lzpel/cloudmama/esp32/components/esp8266-google-home-notifier/src/esp8266-google-home-notifier.h

#ifndef GoogleHomeNotifier_h
#define GoogleHomeNotifier_h

#include <pb.h>
#include <pb_encode.h>
#include <pb_decode.h>
#include <cast_channel.pb.h>

#include <WiFiClientSecure.h>

#include "esp_sdk_version.h"
#ifdef ARDUINO_ARCH_ESP8266
#include <ESP8266mDNS.h>
#elif defined ARDUINO_ARCH_ESP32
#include <ESPmDNS.h>
#else
#error "ARDUINO_ARCH_ESP8266 or ARDUINO_ARCH_ESP32 has to be defined."
#endif

//#include <google-tts.h>

#define LIB_NAME "GoogleHomeNotifier for ESP8266"
#define LIB_VERSION "0.1"

#define APP_ID "CC1AD845"

#define SOURCE_ID "sender-0"
#define DESTINATION_ID "receiver-0"

#define CASTV2_NS_CONNECTION "urn:x-cast:com.google.cast.tp.connection"
#define CASTV2_NS_HEARTBEAT "urn:x-cast:com.google.cast.tp.heartbeat"
#define CASTV2_NS_RECEIVER "urn:x-cast:com.google.cast.receiver"
#define CASTV2_NS_MEDIA "urn:x-cast:com.google.cast.media"

#define CASTV2_DATA_CONNECT "{\"type\":\"CONNECT\"}"
#define CASTV2_DATA_PING "{\"type\":\"PING\"}"
#define CASTV2_DATA_LAUNCH "{\"type\":\"LAUNCH\",\"appId\":\"%s\",\"requestId\":1}"
#define CASTV2_DATA_LOAD "{\"type\":\"LOAD\",\"autoplay\":true,\"currentTime\":0,\"activeTrackIds\":[],\"repeatMode\":\"REPEAT_OFF\",\"media\":{\"contentId\":\"%s\",\"contentType\":\"audio/mp3\",\"streamType\":\"BUFFERED\"},\"requestId\":1}"

typedef class GoogleHomeNotifier {

private:
  char m_transportid[40] = {0};
  char m_clientid[40] = {0};

  //TTS tts;
  WiFiClientSecure* m_client = nullptr;
  boolean m_clientCreated = false;
  IPAddress m_ipaddress;
  uint16_t m_port = 0;
  char m_locale[10] = "en";
  char m_name[128] = "";
  char m_lastError[128] = "";
  bool m_mDNSIsRunning = false;
  static bool encode_string(pb_ostream_t *stream, const pb_field_t *field, void * const *arg);
  static bool decode_string(pb_istream_t *stream, const pb_field_t *field, void **arg);
  boolean connect();
  boolean _play(const char *mp3url);
  void disconnect();
  void setLastError(const char *lastError);
  boolean sendMessage(const char *sourceId, const char *destinationId, const char *ns, const char *data);
  boolean cast(const char *phrase, const char *mp3Url, WiFiClientSecure* pClient = nullptr);

public:
  boolean ip(IPAddress ip, const char *locale = "en", uint16_t port = 8009);
  boolean device(const char *name, const char *locale = "en", int to = 10000);
  boolean notify(const char *phrase, WiFiClientSecure* pClient = nullptr);
  boolean play(const char *mp3Url, WiFiClientSecure* pClient = nullptr);
  const IPAddress getIPAddress();
  const uint16_t getPort();
  const char * getLastError();

} GoogleHomeNotifier;

#endif
