lzpel/cloudmama/esp32/components/esp8266-google-home-notifier/src/esp_sdk_version.h

#ifndef ESP_SDK_VERSION_h
#define ESP_SDK_VERSION_h

//#include <core_version.h>

//#if defined(ARDUINO_ESP32_RELEASE_1_0_4) || defined(ARDUINO_ESP32_RELEASE_1_0_3) || defined(ARDUINO_ESP32_RELEASE_1_0_2) || defined(ARDUINO_ESP32_RELEASE_1_0_1) || defined(ARDUINO_ESP32_RELEASE_1_0_0)
//#define ARDUINO_ESP32_RELEASE_BEFORE_THAN_1_0_5
//#endif

//#if defined(ARDUINO_ESP8266_RELEASE_2_4_2) || defined(ARDUINO_ESP8266_RELEASE_2_4_1) || defined(ARDUINO_ESP8266_RELEASE_2_4_0) || defined(ARDUINO_ESP8266_RELEASE_2_4_0_RC2) || defined(ARDUINO_ESP8266_RELEASE_2_4_0_RC1) || defined(ARDUINO_ESP8266_RELEASE_2_4_0) || defined(ARDUINO_ESP8266_RELEASE_2_3_0) || defined(ARDUINO_ESP8266_RELEASE_2_3_0_RC2)
//#define ARDUINO_ESP8266_RELEASE_BEFORE_THAN_2_5_0
//#endif

#endif
