lzpel/cloudmama/esp32/main/urlencode.h

const char encTable[16] = {
    '0', '1', '2', '3', '4', '5', '6', '7',
    '8', '9', 'a', 'b', 'c', 'd', 'e', 'f'
};
const char safeTable[128] = {
    //      0  1  2  3  4  5  6  7  8  9  A  B  C  D  E  F
    /* 0 */ 0, 0, 0, 0, 0, 0, 0, 0, 0, 0, 0, 0, 0, 0, 0, 0,
    /* 1 */ 0, 0, 0, 0, 0, 0, 0, 0, 0, 0, 0, 0, 0, 0, 0, 0,
    /* 2 */ 0, 0, 0, 0, 0, 0, 0, 0, 0, 0, 0, 0, 0, 0, 0, 0,
    /* 3 */ 1, 1, 1, 1, 1, 1, 1, 1, 1, 1, 0, 0, 0, 0, 0, 0,
    /* 4 */ 0, 1, 1, 1, 1, 1, 1, 1, 1, 1, 1, 1, 1, 1, 1, 1,
    /* 5 */ 1, 1, 1, 1, 1, 1, 1, 1, 1, 1, 1, 0, 0, 0, 0, 0,
    /* 6 */ 0, 1, 1, 1, 1, 1, 1, 1, 1, 1, 1, 1, 1, 1, 1, 1,
    /* 7 */ 1, 1, 1, 1, 1, 1, 1, 1, 1, 1, 1, 0, 0, 0, 0, 0
};
String urlEncode(const char* msg){
    String encoded = "";

    while(*msg != '\0'){
        if(safeTable[int(*msg)]){
            encoded += *msg;
        }
        else{
            encoded += '%';
            encoded += encTable[*msg >> 0x04];
            encoded += encTable[*msg & 0x0F];
        }
        msg++;
    }

    return encoded;
}
